Offenware/Wordclock/Faceplate/Inkscape/wettersnijer.png

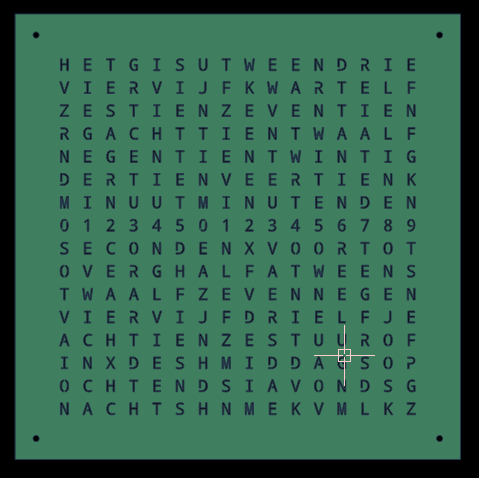
Faceplate/Inkscape/wettersnijer.png
