Offenware/Wordclock/Photos/Knipsel4.PNG

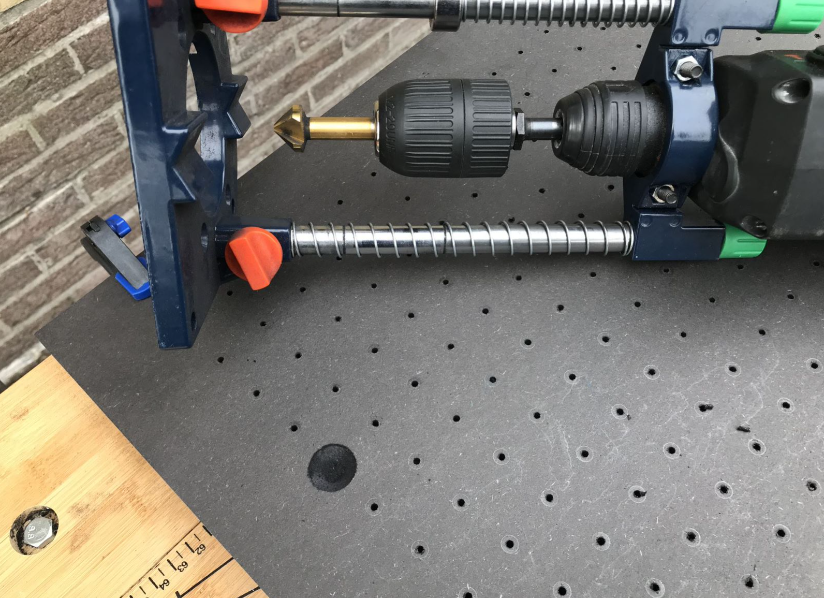
Photos/Knipsel4.PNG
