Offenware/Wordclock/Photos/Knipsel5.PNG

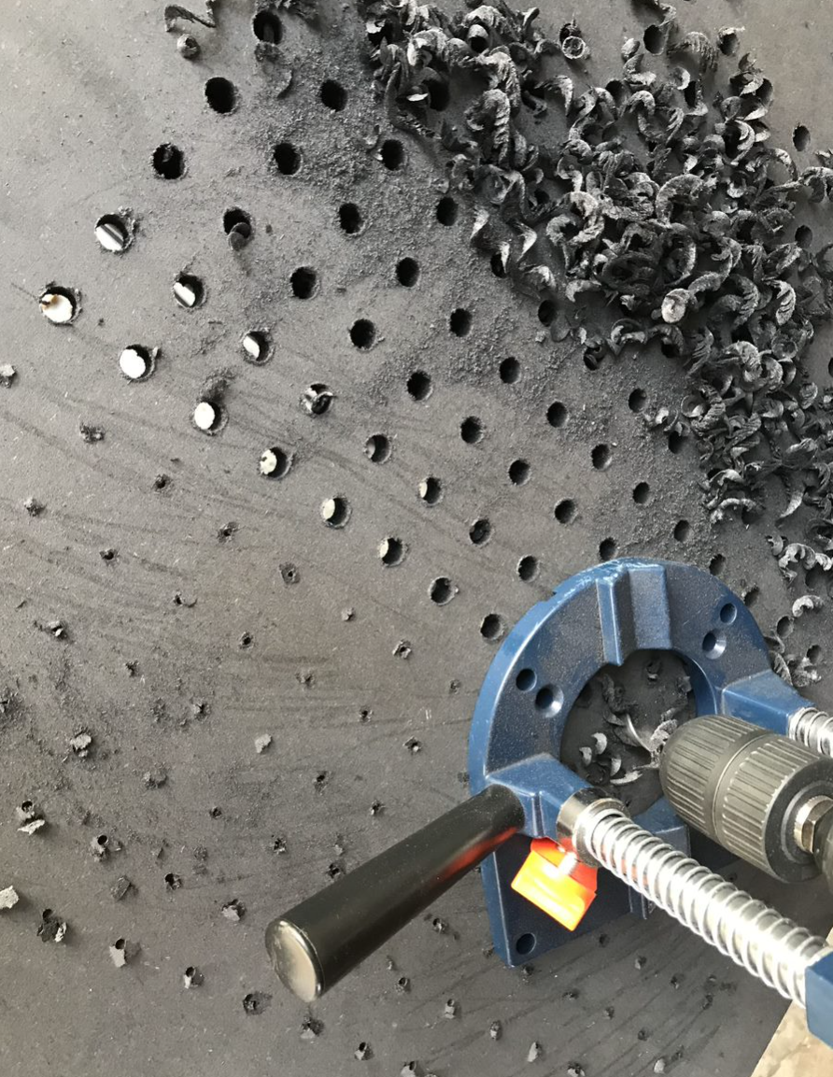
Photos/Knipsel5.PNG
