Offenware/Wordclock/Photos/Knipsel7.PNG

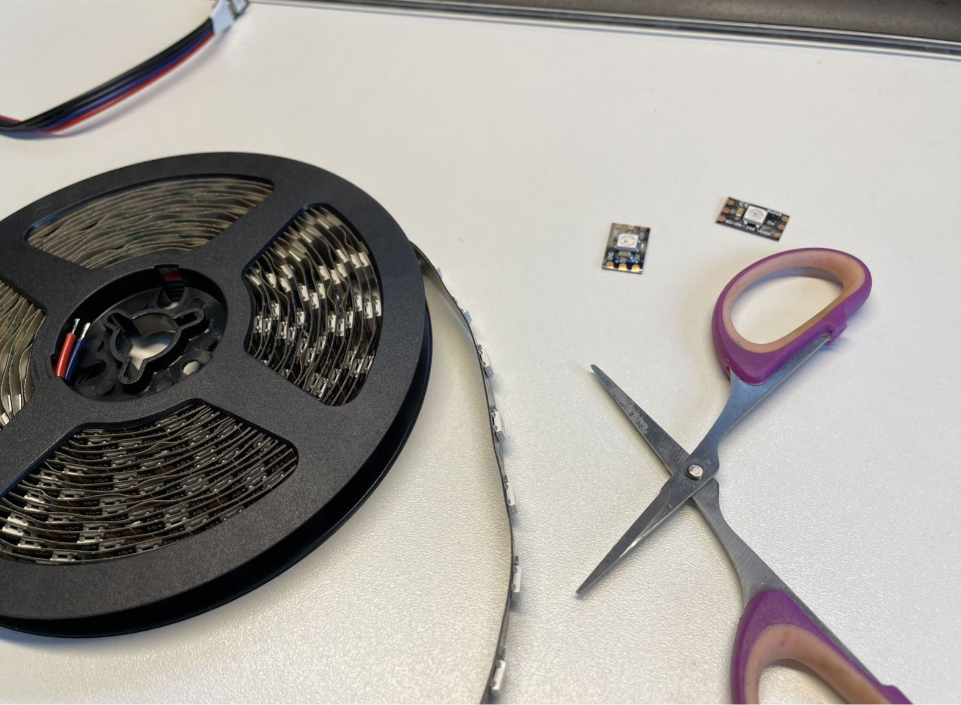
Photos/Knipsel7.PNG
