Offenware/Wordclock/Photos/Knipsel9.PNG

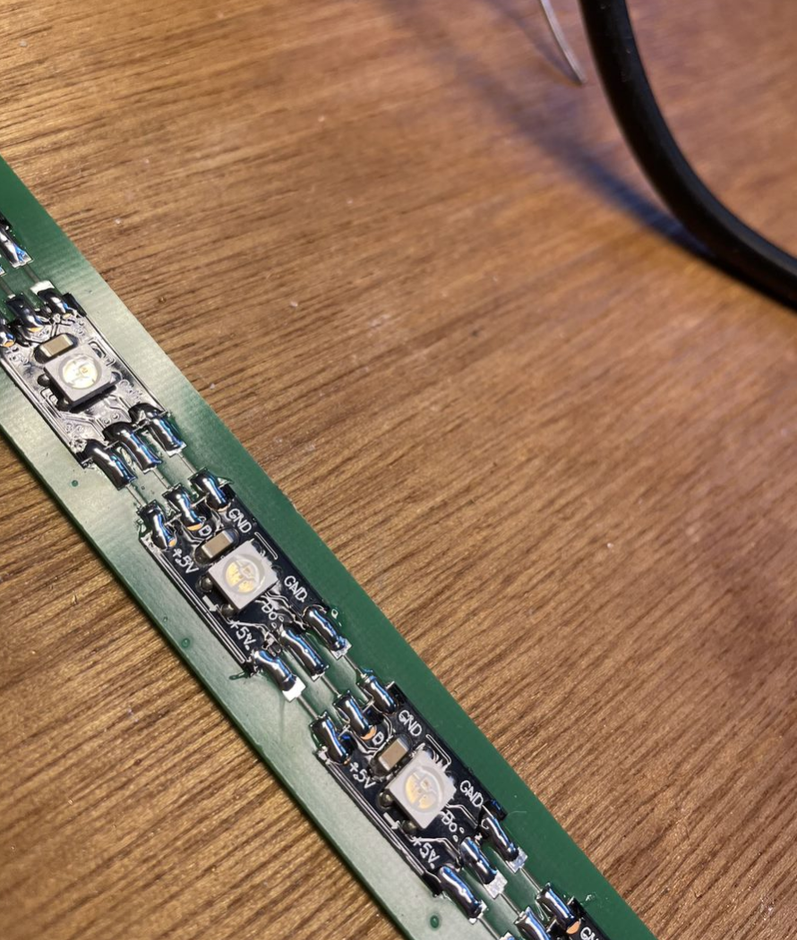
Photos/Knipsel9.PNG
