Offenware/Wordclock/Photos/Knipsel10.PNG

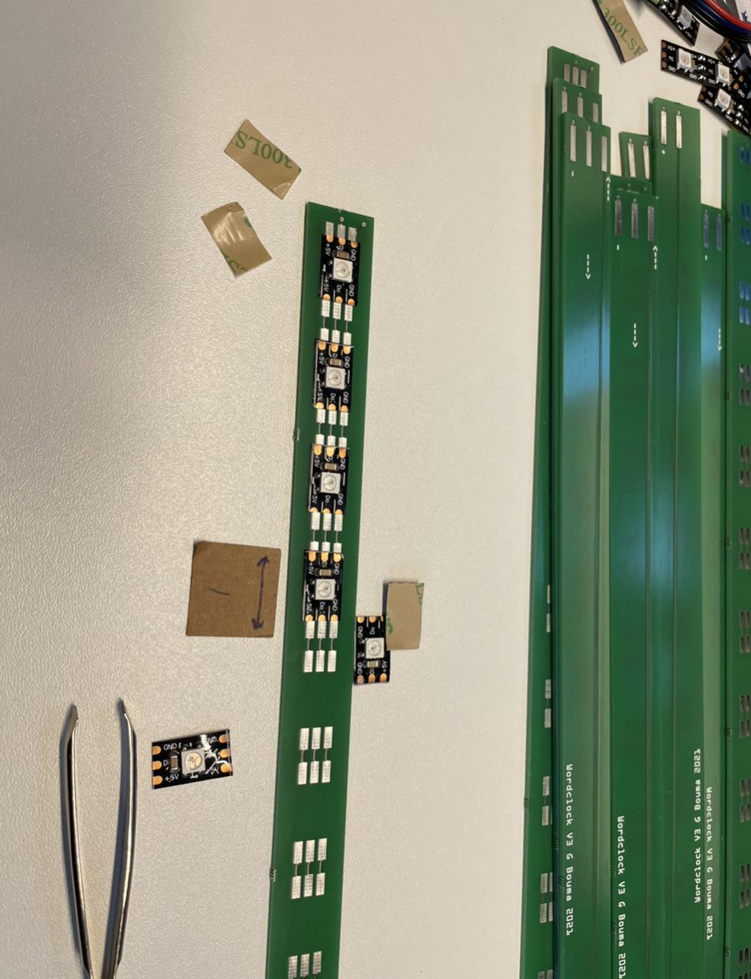
Photos/Knipsel10.PNG
