Offenware/Wordclock/Photos/Knipsel12.PNG

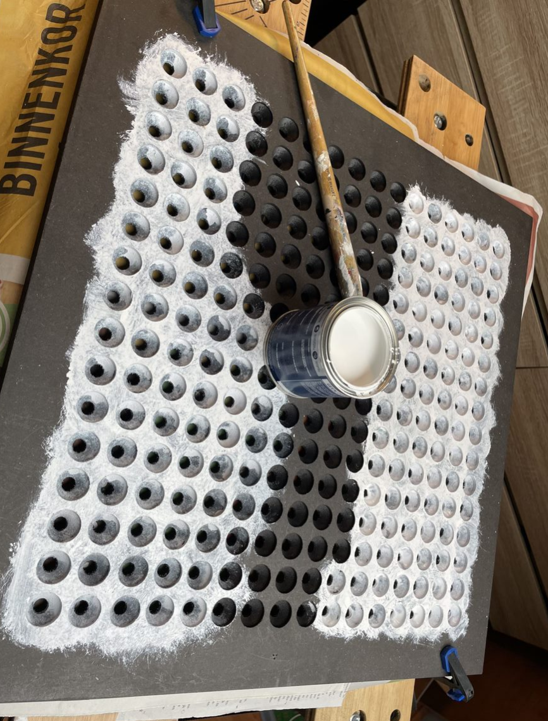
Photos/Knipsel12.PNG
