Offenware/Wordclock/Photos/Knipsel13.PNG

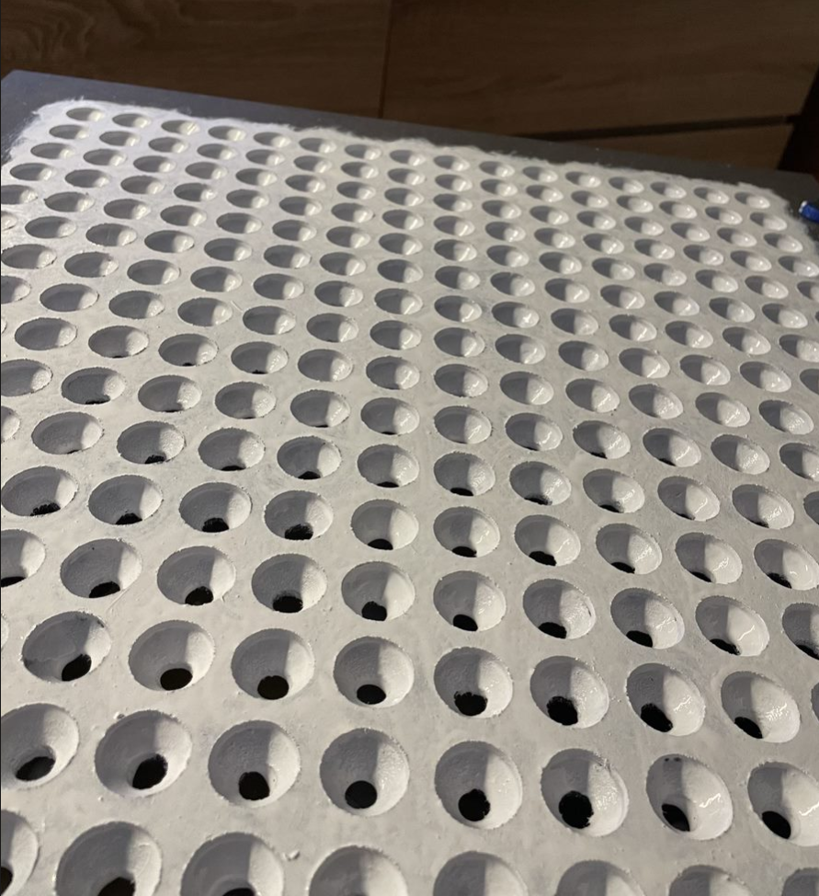
Photos/Knipsel13.PNG
