Offenware/Wordclock/Photos/Knipsel14.PNG

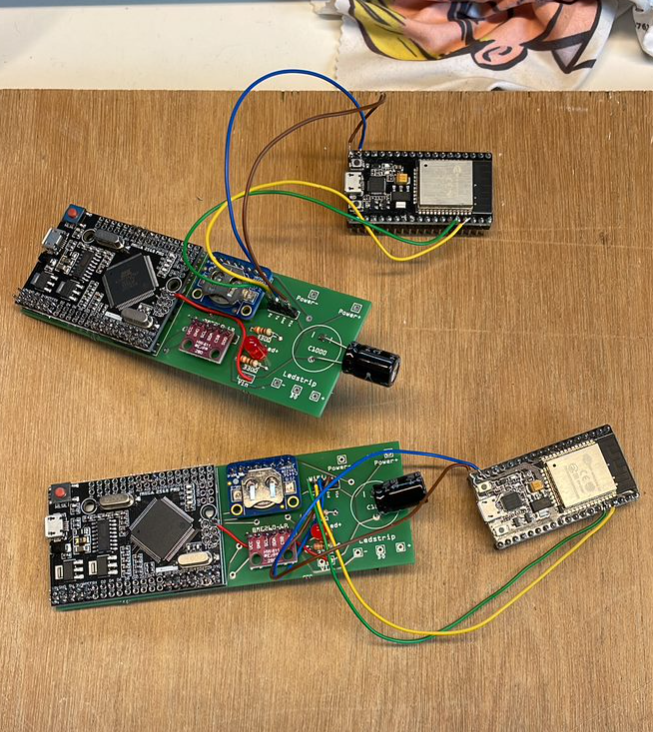
Photos/Knipsel14.PNG
