Offenware/Wordclock/Photos/Knipsel15.PNG

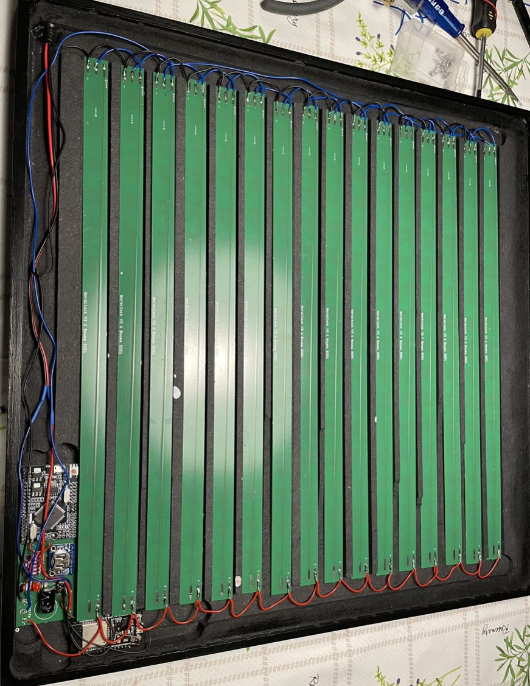
Photos/Knipsel15.PNG
