Offenware/Wordclock/Photos/Knipsel17.PNG

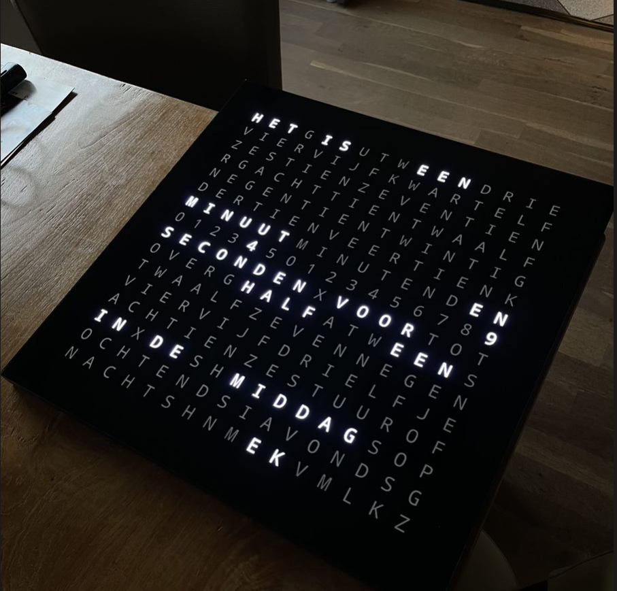
Photos/Knipsel17.PNG
