Offenware/Wordclock/Photos/Knipsel.jpg

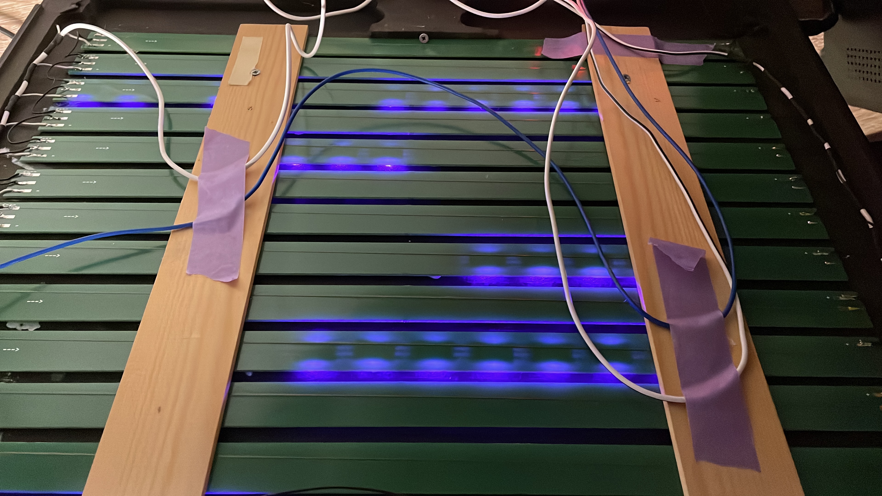
Photos/Knipsel.jpg
