Offenware/Wordclock/Photos/Knipsel.PNG

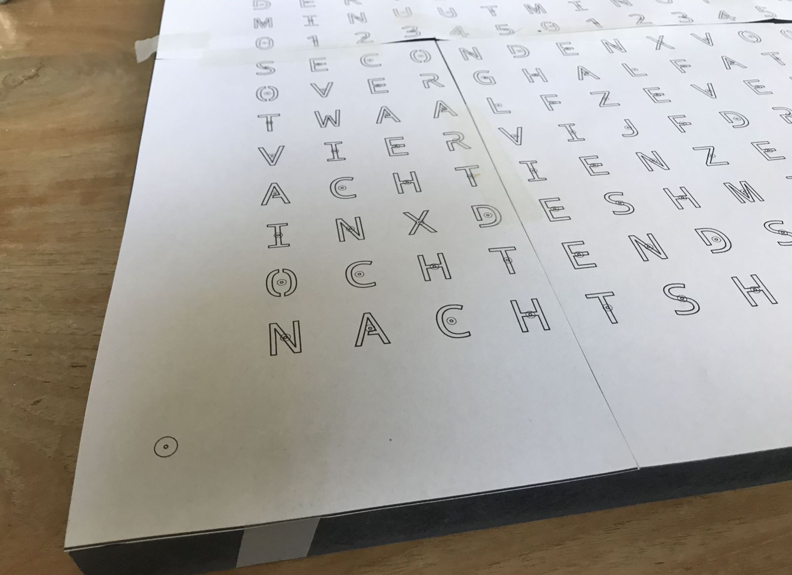
Photos/Knipsel.PNG
