Offenware/Wordclock/Wordclock_Gerhard_WiFi/nodemcu esp32-s 38 pins .jpg

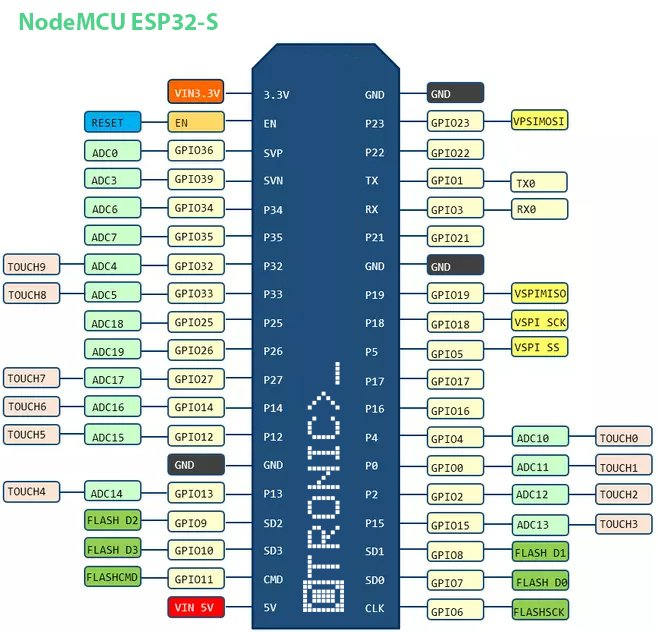
Wordclock_Gerhard_WiFi/nodemcu esp32-s 38 pins .jpg
