Offenware/Wordclock/Wordclock_Gerhard_Mega/nederlands.h

#ifndef nederlands_h
#define nederlands_h

#include "MoonPhase.h"
#include "wordclock.h"

// In het LED array zitten de lage bit links ipv rechts, dus alles achterstevoren zetten en dan hex waarde berekenen
#define NL_HET          {0, 0x0007} //1110 0000 0000 0000 -> 0000 0000 0000 0111 : 0007
#define NL_IS           {0, 0x0030} //0000 1100 0000 0000 -> 0000 0000 0011 0000 : 0030
#define NL_M_EEN        {0, 0x0E00} //0000 0000 0111 0000 -> 0000 1110 0000 0000 : 0E00
#define NL_M_TWEE       {0, 0x0780} //0000 0001 1110 0000 -> 0000 0111 1000 0000 : 0780
#define NL_M_DRIE       {0, 0xF000} //0000 0000 0000 1111 -> 1111 0000 0000 0000 : F000

#define NL_M_VIER       {1, 0x000F} //1111 0000 0000 0000 -> 0000 0000 0000 1111 : 000F
#define NL_M_VIJF       {1, 0x00F0} //0000 1111 0000 0000 -> 0000 0000 1111 0000 : 00F0
#define NL_M_KWART      {1, 0x1F00} //0000 0000 1111 1000 -> 0001 1111 0000 0000 : 1F00
#define NL_M_ELF        {1, 0xE000} //0000 0000 0000 0111 -> 1110 0000 0000 0000 : E000

#define NL_M_ZES        {2, 0x0007} //1110 0000 0000 0000 -> 0000 0000 0000 0111 : 0007
#define NL_M_ZESTIEN    {2, 0x007F} //1111 1110 0000 0000 -> 0000 0000 0111 1111 : 007F
#define NL_M_ZEVEN      {2, 0x0F80} //0000 0001 1111 0000 -> 0000 1111 1000 0000 : 0F80
#define NL_M_ZEVENTIEN  {2, 0xFF80} //0000 0001 1111 1111 -> 1111 1111 1000 0000 : FF80

#define NL_M_ACHT       {3, 0x003C} //0011 1100 0000 0000 -> 0000 0000 0011 1100 : 003C
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
boolean bepaalZomertijd(int jaar, int maand, int dag);
int bepaalWeekdag(int jaar, int maand, int dag);

#endif
